redglitch2/FrameDeck/Step Files Rev.1/Start_Brace.step

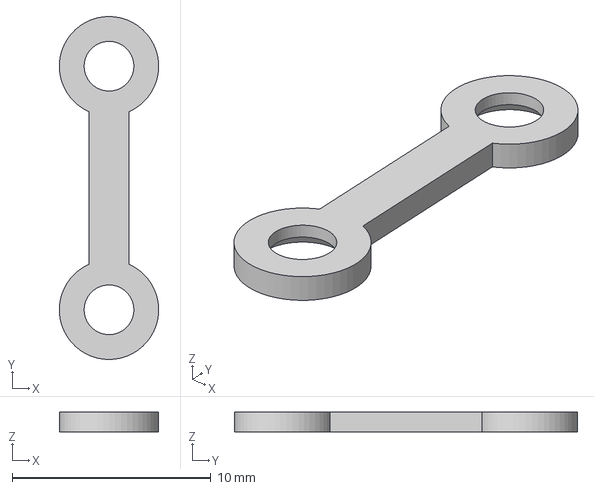
[picture p15: CAD file, 2024-01-26]
Step Files Rev.1/Start_Brace.step
5.00 x 17.2 x 1.00 mm
