redglitch2/FrameDeck/Step Files Rev.1/Select_Brace.step

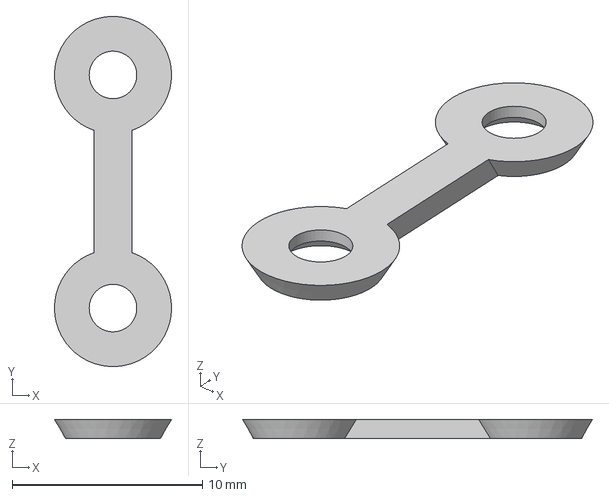
[picture p16: CAD file, 2024-01-26]
Step Files Rev.1/Select_Brace.step
6.15 x 18.4 x 1.00 mm
