redglitch2/FrameDeck/Step Files Rev.1/Screen_Brace_Right.step

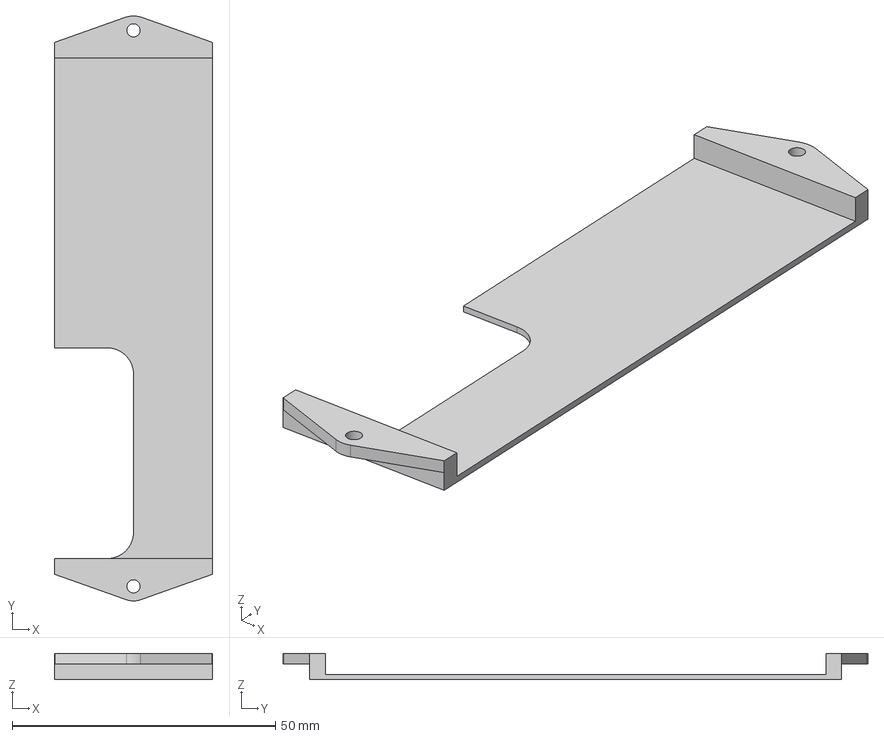
[picture p17: CAD file, 2024-01-26]
Step Files Rev.1/Screen_Brace_Right.step
30.0 x 111.0 x 5.00 mm
